Polypheides/SDcard-reader-Thinkpad-T14-21CG/Misc/Images/2D_PCB_PCB_SD-pcb-t14-rev-2_2026-01-31_2026-02-15_btm.png

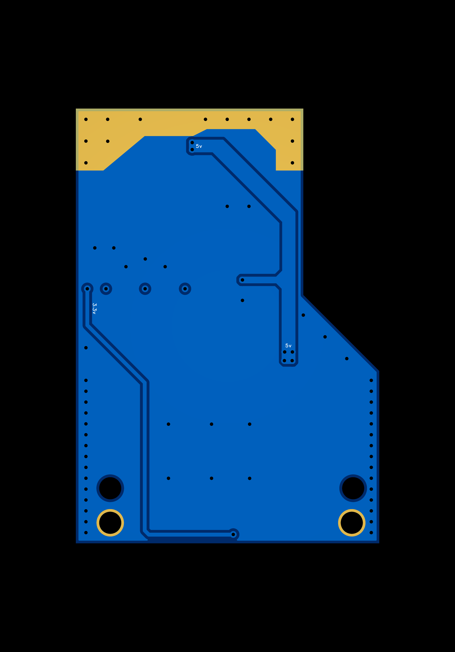
Misc/Images/2D_PCB_PCB_SD-pcb-t14-rev-2_2026-01-31_2026-02-15_btm.png
