Polypheides/SDcard-reader-Thinkpad-T14-21CG/Misc/Images/5v-guessing.png

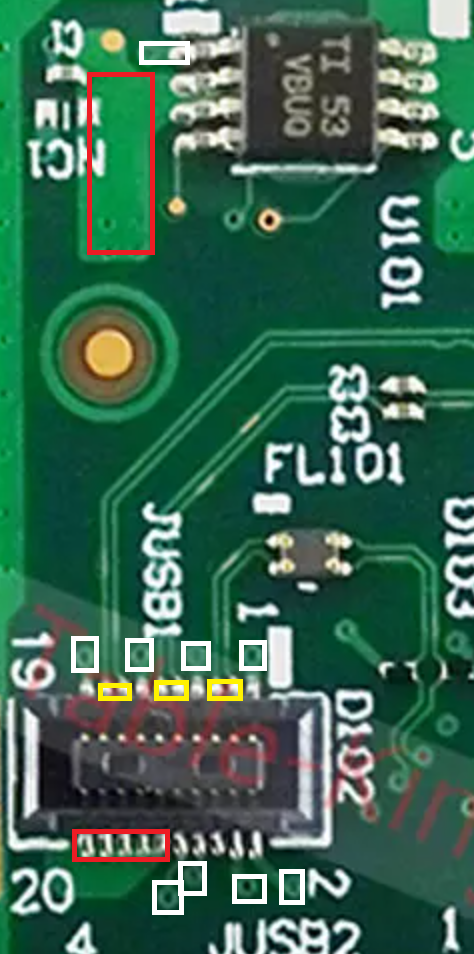
Misc/Images/5v-guessing.png
