Polypheides/SDcard-reader-Thinkpad-T14-21CG/Misc/Images/consept-of-Rev-5.png

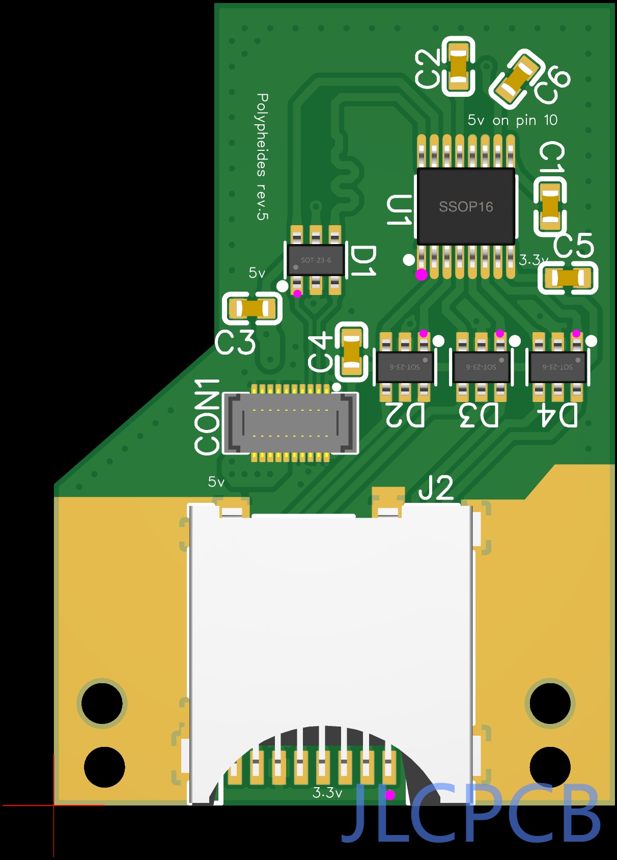
Misc/Images/consept-of-Rev-5.png
