Polypheides/SDcard-reader-Thinkpad-T14-21CG/Misc/Images/data-pin-guessing.png

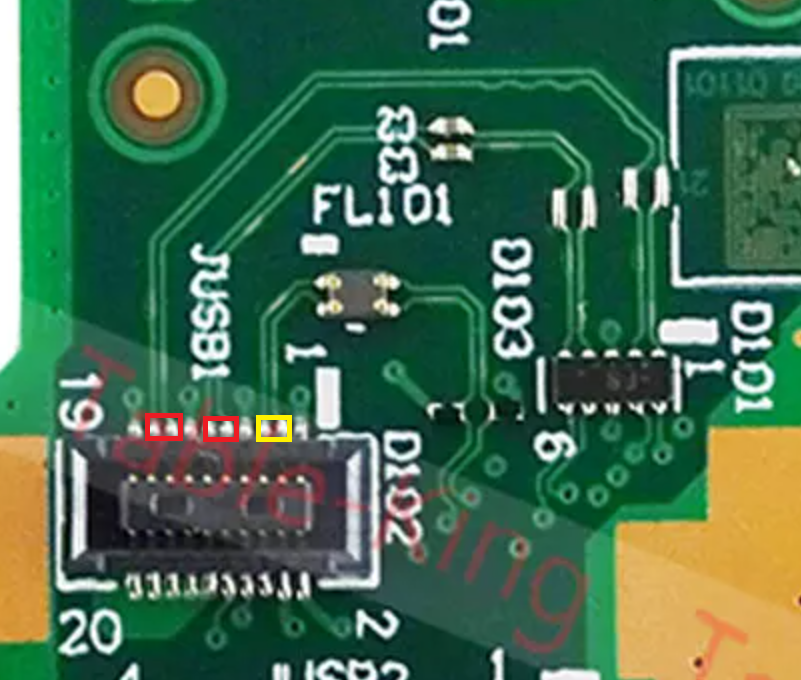
Misc/Images/data-pin-guessing.png
