Polypheides/SDcard-reader-Thinkpad-T14-21CG/Misc/Images/Rev. 7 Fitment.jpg

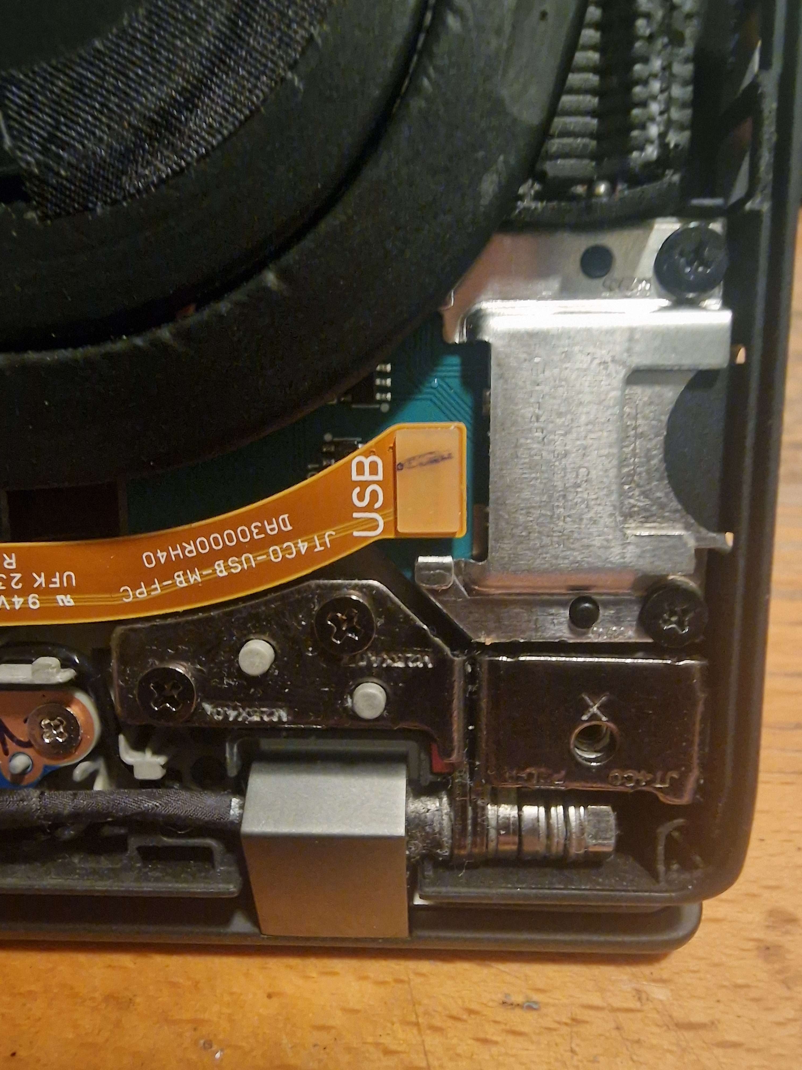
Misc/Images/Rev. 7 Fitment.jpg
