Polypheides/SDcard-reader-Thinkpad-T14-21CG/Misc/Images/Rev. 7 SDcard slot fitment.jpg

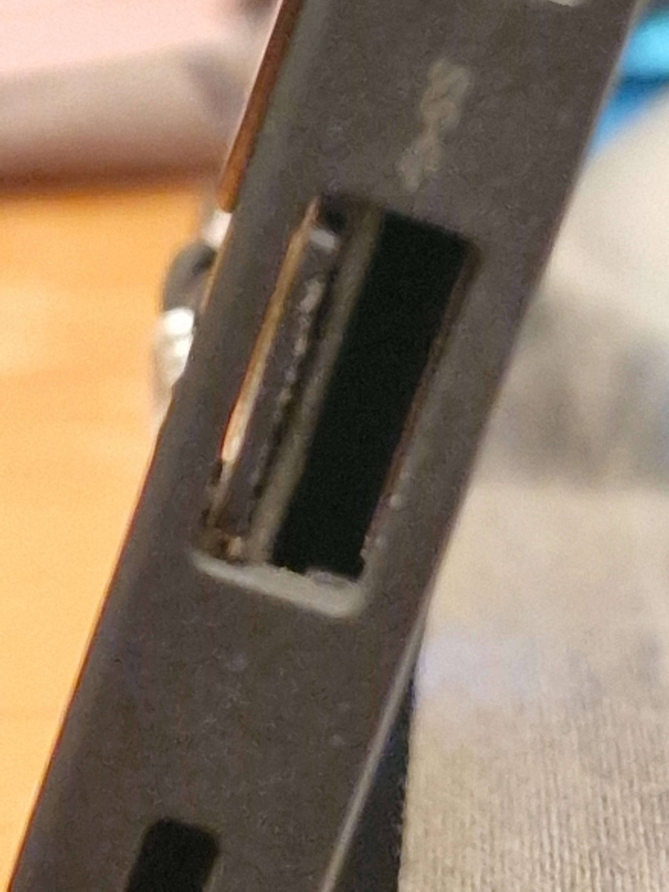
Misc/Images/Rev. 7 SDcard slot fitment.jpg
