Polypheides/SDcard-reader-Thinkpad-T14-21CG/Misc/Images/Untitled.png

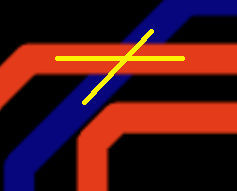
Misc/Images/Untitled.png
