Polypheides/SDcard-reader-Thinkpad-T14-21CG/Misc/Images/USB board Flex Ribbon Cable for LENOVO ThinkPad T14 Gen 4 21HD 21HE 21K3 21K4.webp

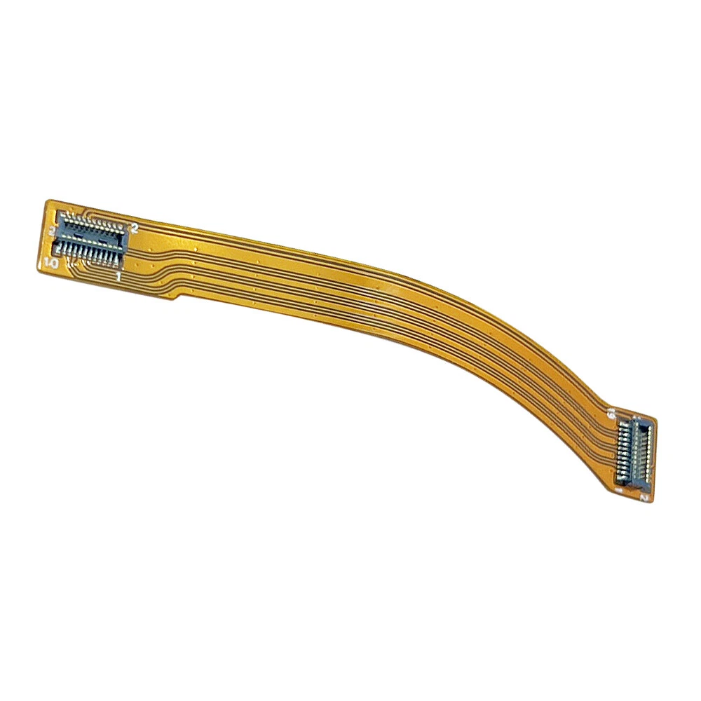
Misc/Images/USB board Flex Ribbon Cable for LENOVO ThinkPad T14 Gen 4 21HD 21HE 21K3 21K4.webp
